e3donline/Motion-System/STPs/MS-X-BELT-PLATE 1.6.step

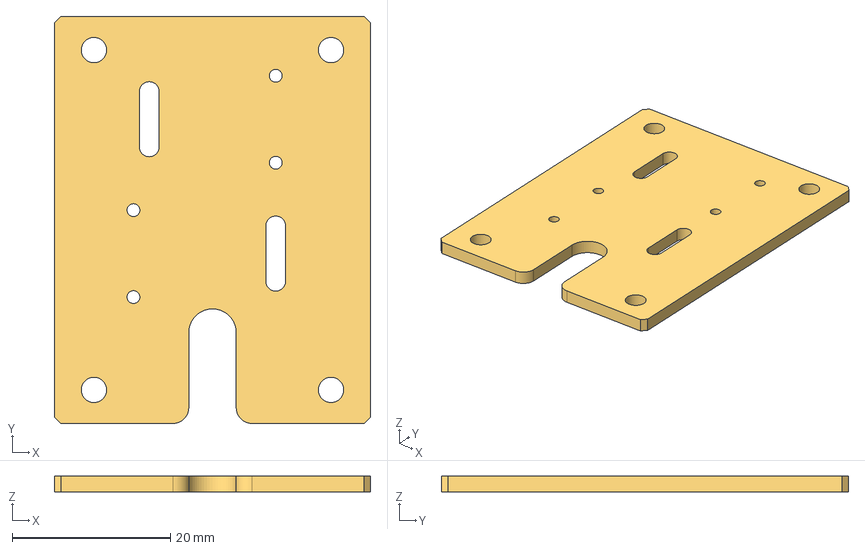
[picture p15: CAD file, 2019-07-30]
STPs/MS-X-BELT-PLATE 1.6.step
40.0 x 51.5 x 2.00 mm
