e3donline/Motion-System/STPs/MS-MOTOR-SPACE-LONG 1.1.step

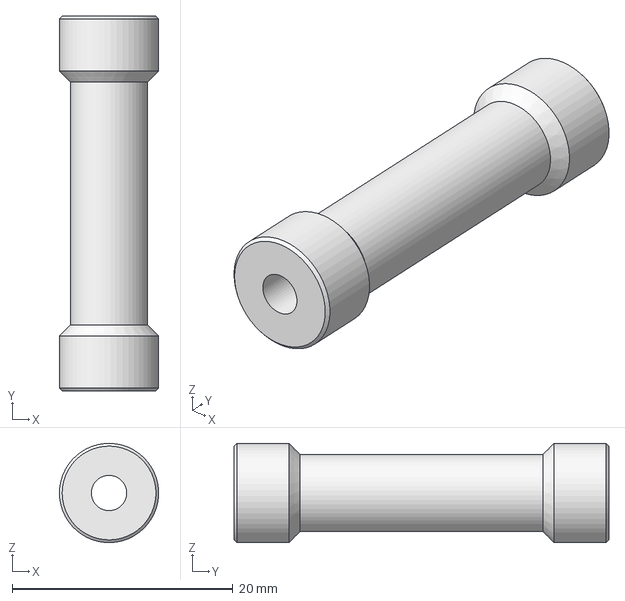
[picture p16: CAD file, 2019-07-30]
STPs/MS-MOTOR-SPACE-LONG 1.1.step
8.99 x 34.0 x 9.00 mm
