e3donline/Motion-System/STPs/MS-TENSION-BLOCK 1.1.step

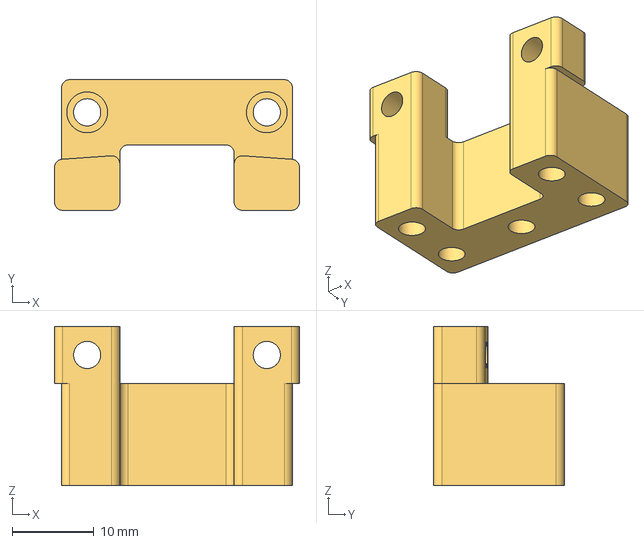
[picture p17: CAD file, 2019-07-30]
STPs/MS-TENSION-BLOCK 1.1.step
30.0 x 16.0 x 19.5 mm
