e3donline/Motion-System/STPs/MS-XY-STOP 1.1.step

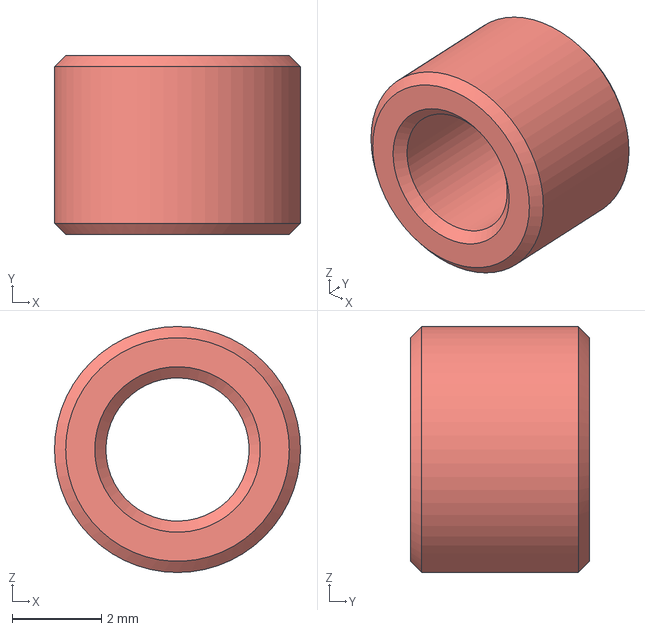
[picture p18: CAD file, 2019-07-30]
STPs/MS-XY-STOP 1.1.step
5.50 x 4.00 x 5.50 mm
