e3donline/Motion-System/STPs/MS-X-BLOCK 1.3.step

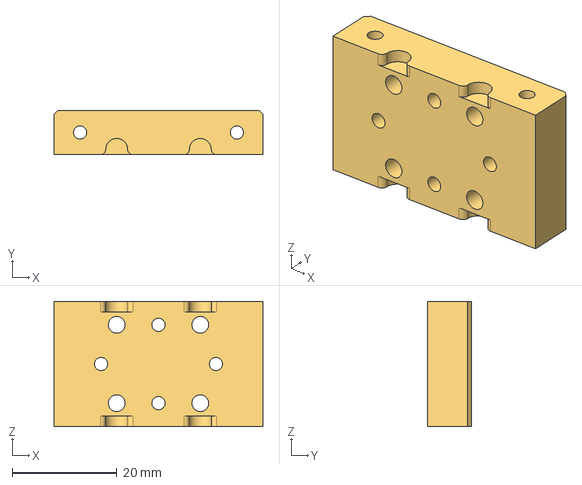
[picture p19: CAD file, 2019-07-30]
STPs/MS-X-BLOCK 1.3.step
40.0 x 8.50 x 24.0 mm
