e3donline/Motion-System/STPs/MS-X-BAR-ALU 1.3.step

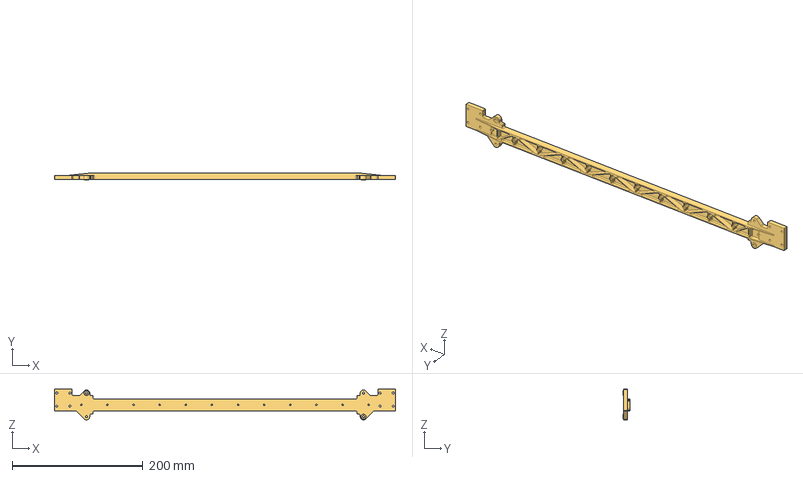
[picture p20: CAD file, 2019-07-30]
STPs/MS-X-BAR-ALU 1.3.step
522.0 x 10.5 x 47.2 mm
