e3donline/Motion-System/STPs/MS-BASE-PLATE 1.4.step

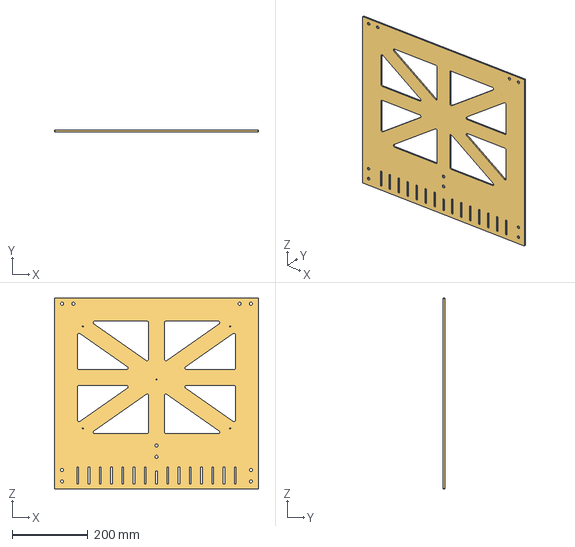
[picture p21: CAD file, 2019-07-30]
STPs/MS-BASE-PLATE 1.4.step
540.0 x 4.00 x 505.0 mm
