e3donline/Motion-System/STPs/MS-BELT-CLAMP-IM 1.2.step

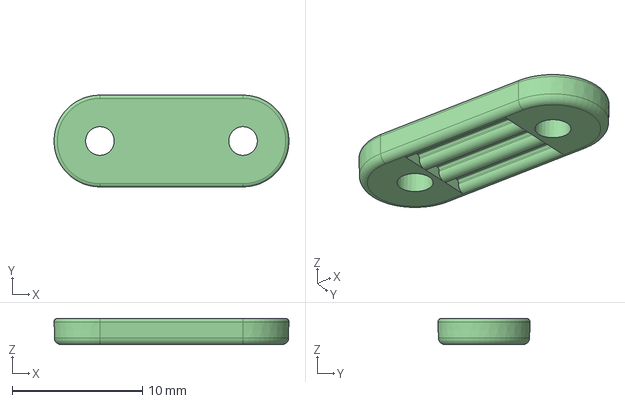
[picture p22: CAD file, 2019-07-30]
STPs/MS-BELT-CLAMP-IM 1.2.step
18.1 x 7.06 x 2.00 mm
