e3donline/Motion-System/STPs/MS-LONG-PULLEY-STANDOFF 1.3.step

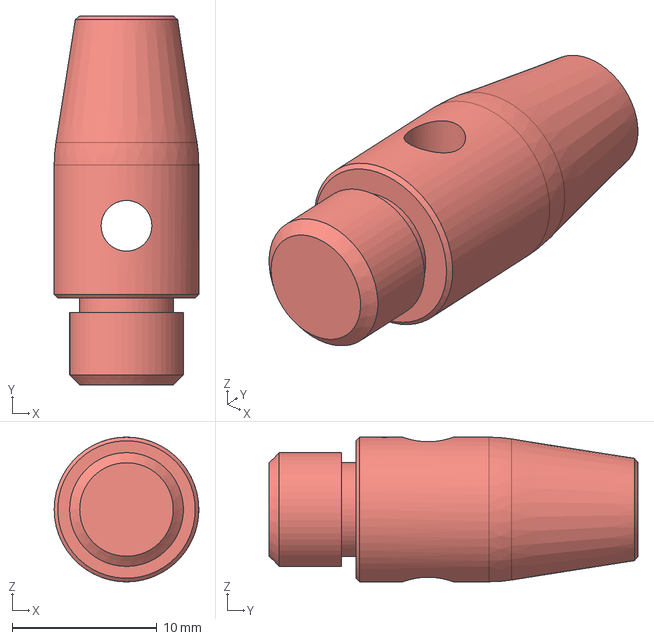
[picture p23: CAD file, 2019-07-30]
STPs/MS-LONG-PULLEY-STANDOFF 1.3.step
10.0 x 25.5 x 10.0 mm
