e3donline/Motion-System/STPs/MS-MOTOR-SPACE-SHORT 1.1.step

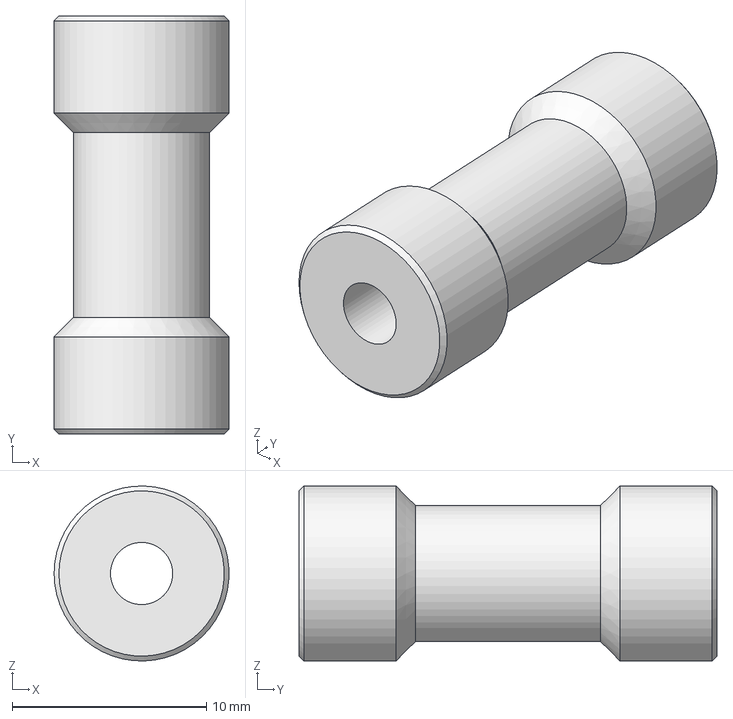
[picture p24: CAD file, 2019-07-30]
STPs/MS-MOTOR-SPACE-SHORT 1.1.step
8.99 x 21.5 x 9.00 mm
