e3donline/Motion-System/STPs/MS-X-SPACER 1.1.step

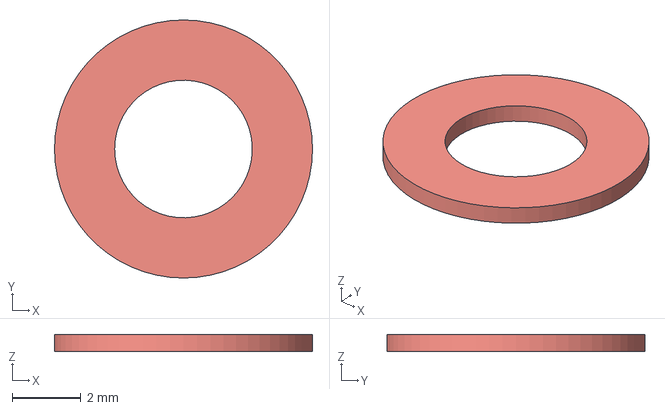
[picture p25: CAD file, 2019-07-30]
STPs/MS-X-SPACER 1.1.step
7.50 x 7.50 x 0.5 mm
