e3donline/Motion-System/STPs/MS-BED-BRACKET 1.4.step

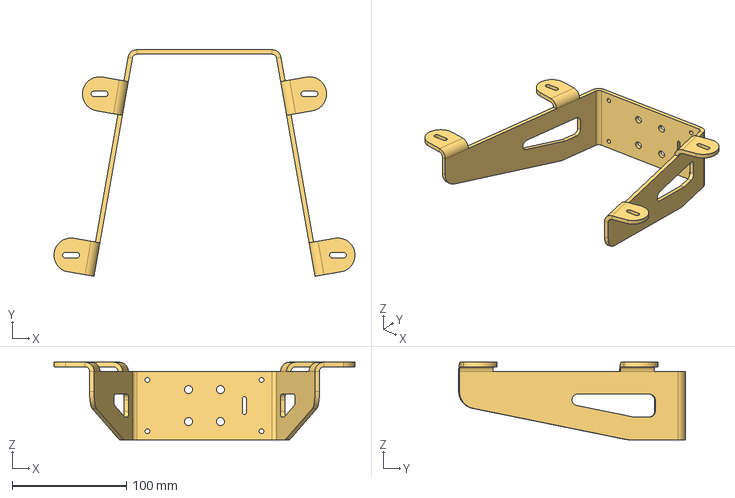
[picture p26: CAD file, 2019-07-30]
STPs/MS-BED-BRACKET 1.4.step
263.8 x 198.6 x 68.0 mm
