e3donline/Motion-System/STPs/MS-SHORT-PULLEY-STANDOFF 1.3.step

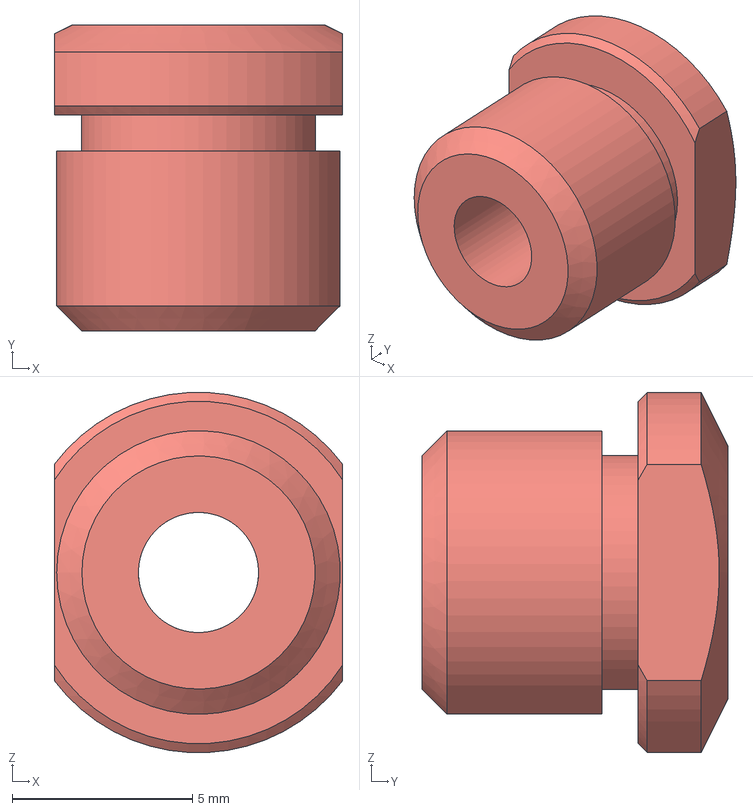
[picture p27: CAD file, 2019-07-30]
STPs/MS-SHORT-PULLEY-STANDOFF 1.3.step
8.00 x 8.50 x 9.99 mm
