e3donline/Motion-System/STPs/MS-Z-STOP 1.0.step

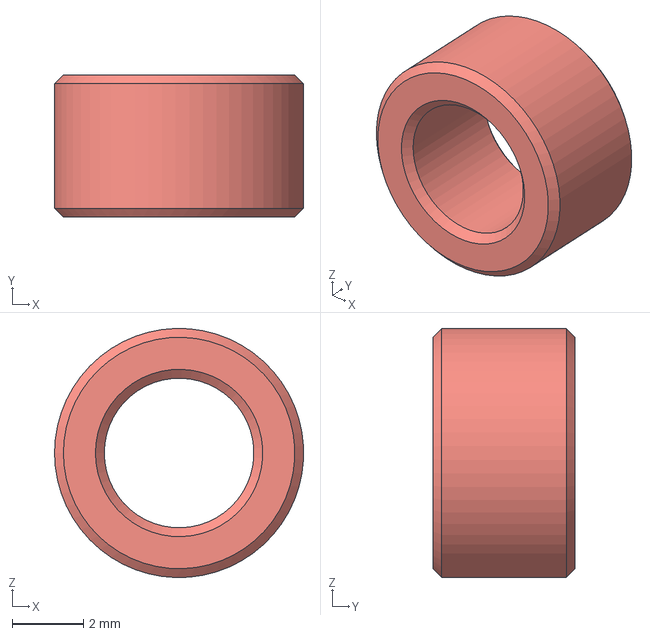
[picture p28: CAD file, 2019-07-30]
STPs/MS-Z-STOP 1.0.step
6.99 x 4.00 x 7.00 mm
