e3donline/Motion-System/STPs/MS-TOP-PLATE 1.6.step

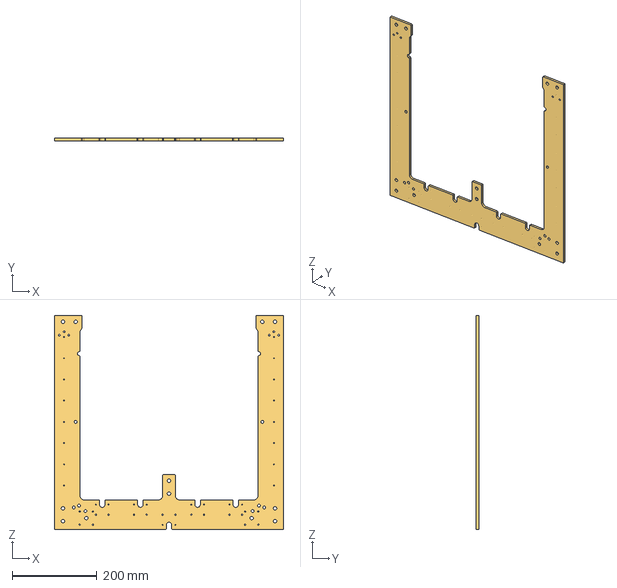
[picture p29: CAD file, 2019-07-30]
STPs/MS-TOP-PLATE 1.6.step
540.0 x 6.00 x 505.0 mm
