e3donline/Motion-System/STPs/MS-TENSION-ARM 1.0.step

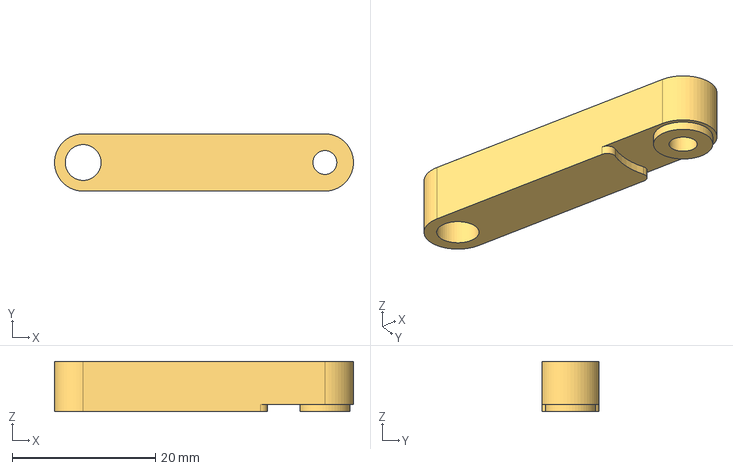
[picture p30: CAD file, 2019-07-30]
STPs/MS-TENSION-ARM 1.0.step
41.8 x 8.00 x 7.00 mm
