e3donline/Motion-System/STPs/MS-Z-MOTOR-BRACKET 1.1.step

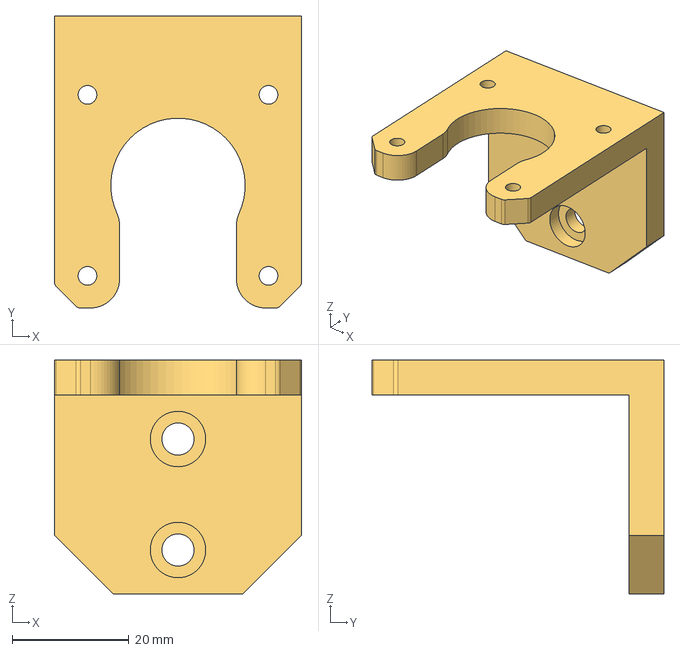
[picture p31: CAD file, 2019-07-30]
STPs/MS-Z-MOTOR-BRACKET 1.1.step
42.3 x 50.0 x 40.0 mm
