e3donline/Motion-System/STPs/MS-BED-PLATE 1.3.step

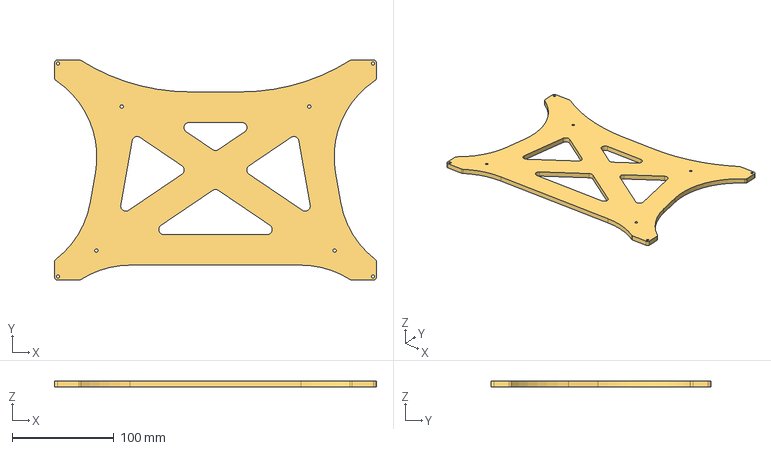
[picture p32: CAD file, 2019-07-30]
STPs/MS-BED-PLATE 1.3.step
316.0 x 216.0 x 6.00 mm
