e3donline/Motion-System/STPs/MS-SOFF-M3-FF-24L 1.1.step

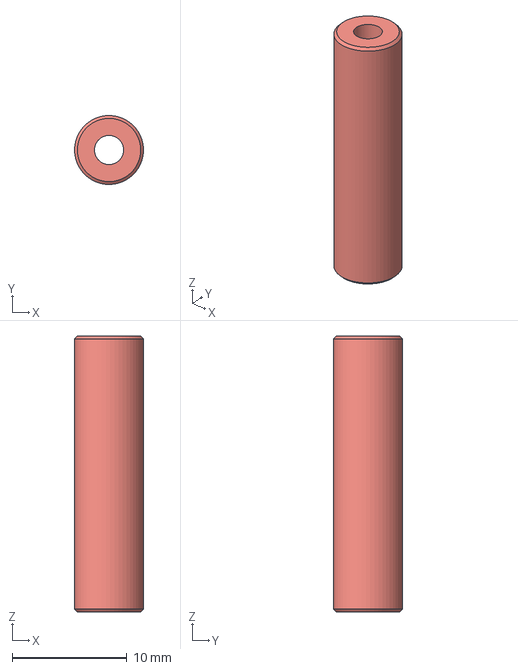
[picture p33: CAD file, 2019-07-30]
STPs/MS-SOFF-M3-FF-24L 1.1.step
5.99 x 6.00 x 24.0 mm
