e3donline/Motion-System/PDFs/MS-SHAFT-BOLT v1.4.pdf

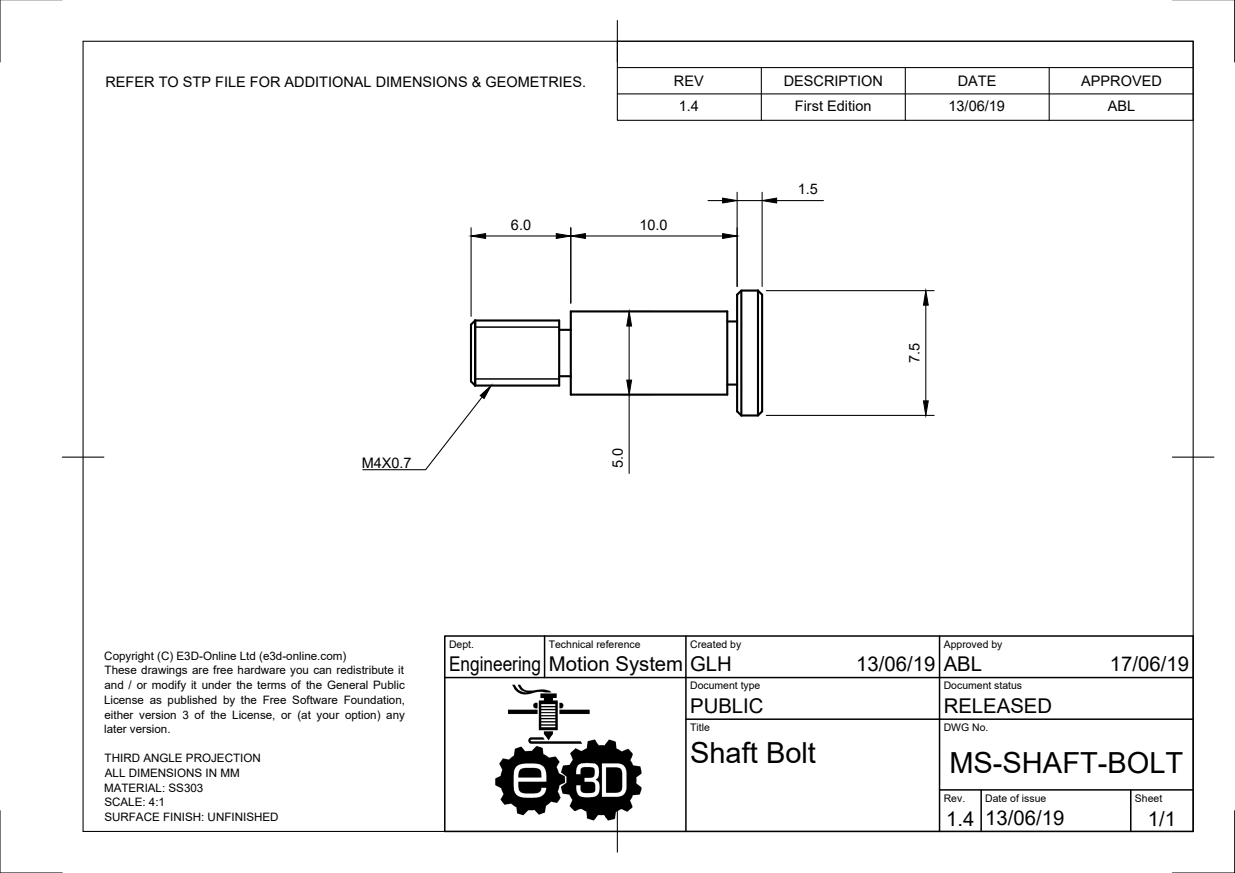
[picture p47: page 1]
First Edition; ABL 7.5

REFER TO STP FILE FOR ADDITIONAL DIMENSIONS & GEOMETRIES.

Dept. Engineering | Technical reference Motion System | Created by GLH 13/06/19 | Approved by ABL Copyright (C) E3D-Online Ltd (e3d-online.com) 17/06/19

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

Document type PUBLIC | Document status RELEASED

Title | DWG No. MS-SHAFT-BOLT Shaft Bolt

THIRD ANGLE PROJECTION
ALL DIMENSIONS IN MM
MATERIAL: SS303
SCALE: 4:1
SURFACE FINISH: UNFINISHED

Rev. 1.4 | Date of issue 13/06/19 | Sheet 1/1
