e3donline/Motion-System/PDFs/MS-TENSION-ARM v1.0.pdf

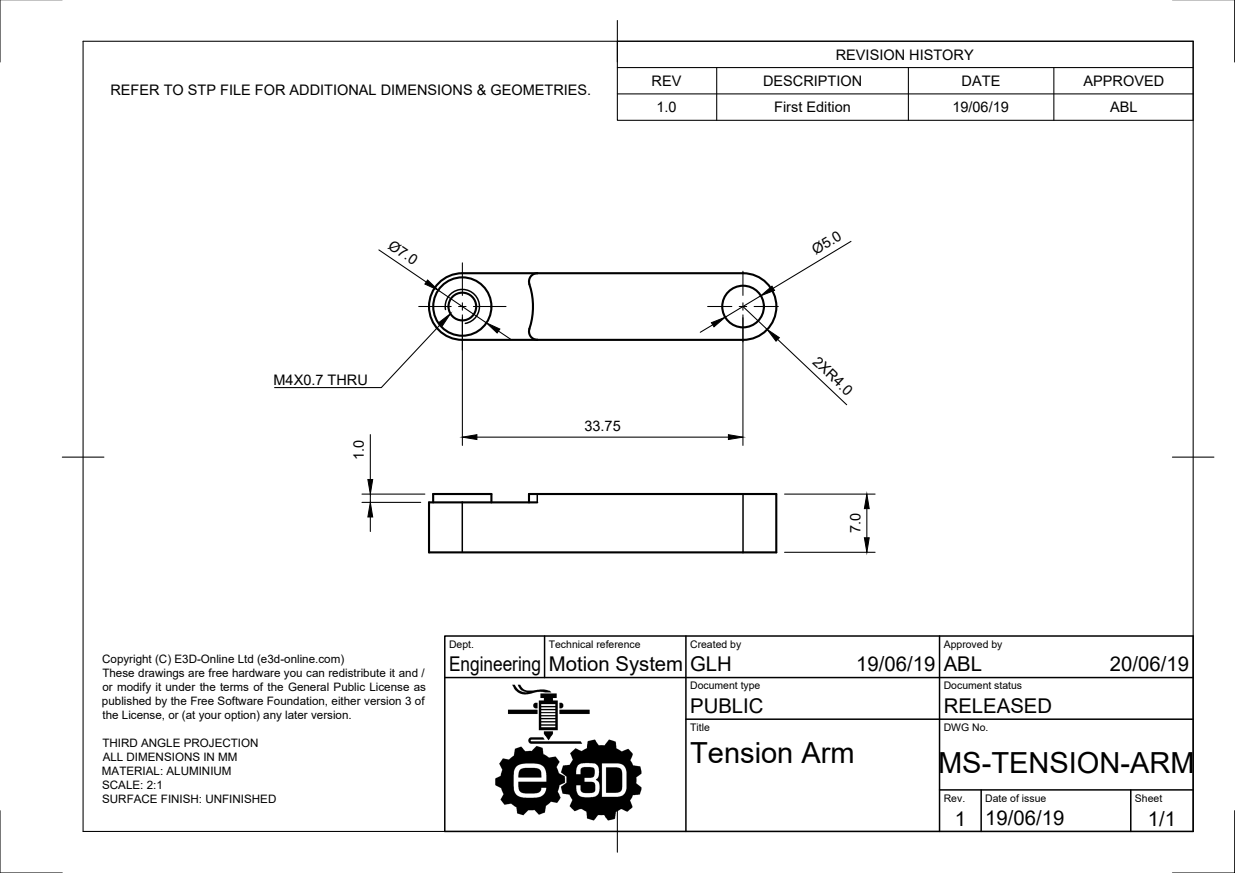
[picture p48: page 1]
M4X0.7 THRU

REVISION HISTORY

REV | DESCRIPTION | DATE | APPROVED
1.0 | First Edition | 19/06/19 | ABL

REFER TO STP FILE FOR ADDITIONAL DIMENSIONS & GEOMETRIES.

Dept. Engineering | Technical reference Motion System | Created by GLH 19/06/19 | Approved by ABL 20/06/19

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

Document type PUBLIC | Document status RELEASED

the License, or (at your option) any later version.

Title Tension Arm | DWG No. MS-TENSION-ARM

THIRD ANGLE PROJECTION
ALL DIMENSIONS IN MM
MATERIAL: ALUMINIUM
SCALE: 2:1
SURFACE FINISH: UNFINISHED

Rev. 1 | Date of issue 19/06/19 | Sheet 1/1
