e3donline/Motion-System/PDFs/MS-TOP-PLATE v1.6.pdf

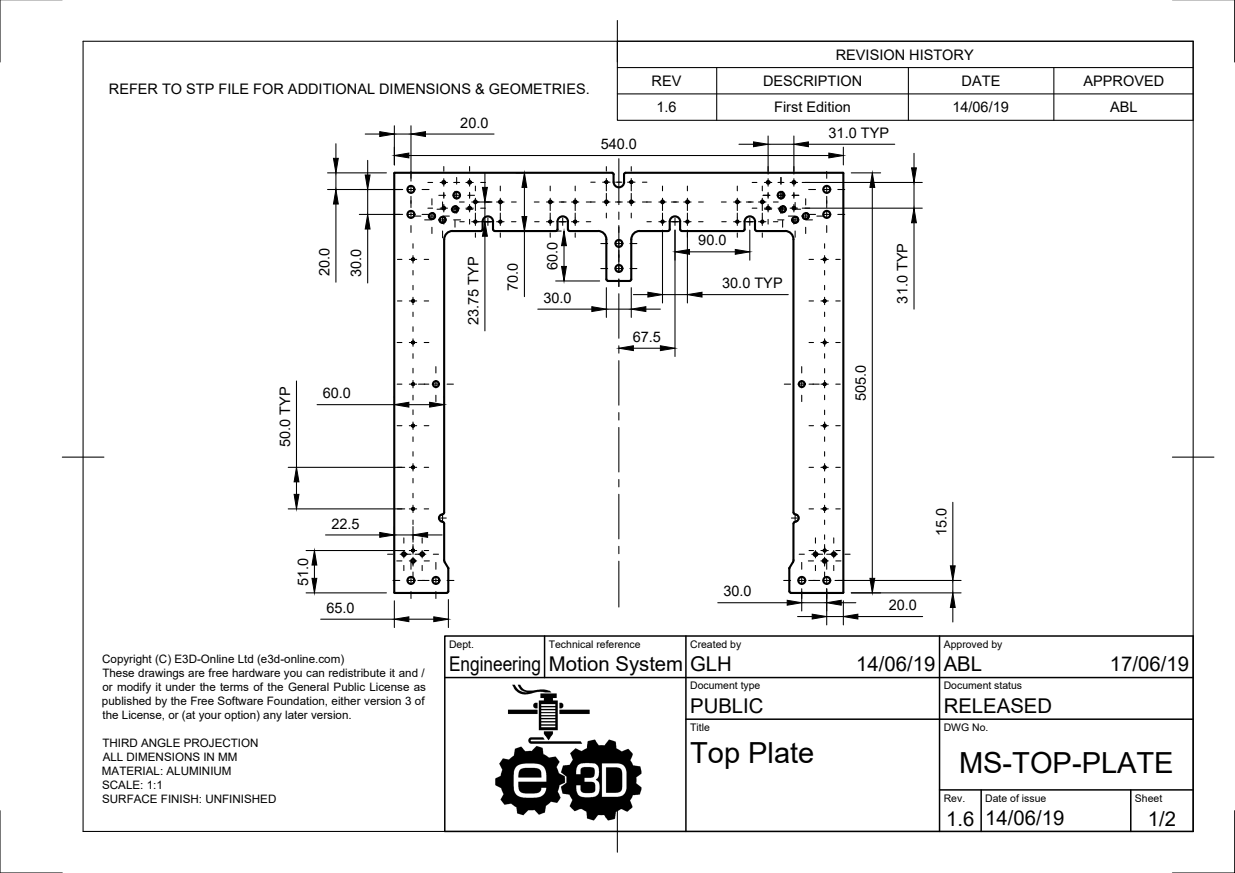
[picture p49: page 1]
90.0 50.0 TYP; 67.5 60.0 23.75 TYP

REVISION HISTORY

REV | DESCRIPTION | DATE | APPROVED
1.6 | First Edition | 14/06/19 | ABL

REFER TO STP FILE FOR ADDITIONAL DIMENSIONS & GEOMETRIES.

31.0 TYP 31.0 TYP 30.0 TYP

Dept. Engineering | Technical reference Motion System | Created by GLH 14/06/19 | Approved by ABL 17/06/19

Copyright (C) E3D-Online Ltd (e3d-online.com)
These drawings are free hardware you can redistribute it and / or modify it under the terms of the General Public License as published by the Free Software Foundation, either version 3 of

Document type PUBLIC | Document status RELEASED

the License, or (at your option) any later version.

Title | DWG No. MS-TOP-PLATE Top Plate

THIRD ANGLE PROJECTION
ALL DIMENSIONS IN MM
MATERIAL: ALUMINIUM
SCALE: 1:1
SURFACE FINISH: UNFINISHED

Rev. 1.6 | Date of issue 14/06/19 | Sheet 1/2

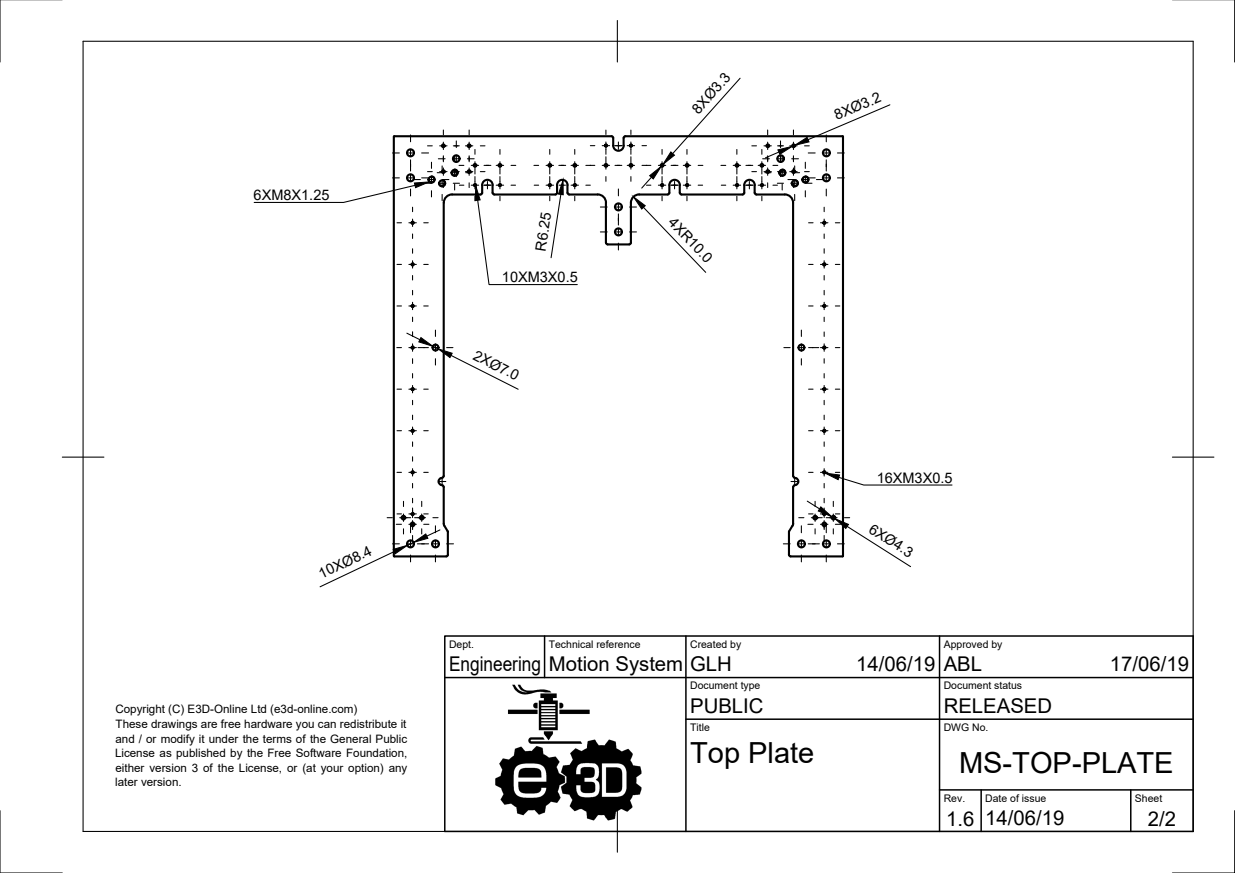
[picture p50: page 2]
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

Document type PUBLIC | Document status RELEASED

Copyright (C) E3D-Online Ltd (e3d-online.com)
These drawings are free hardware you can redistribute it
and / or modify it under the terms of the General Public
License as published by the Free Software Foundation,
either version 3 of the License, or (at your option) any
later version.

Title | DWG No. MS-TOP-PLATE Top Plate

Rev. 1.6 | Date of issue 14/06/19 | Sheet 2/2
