e3donline/Motion-System/PDFs/MS-Z-NUT-BRACKET v1.3.pdf

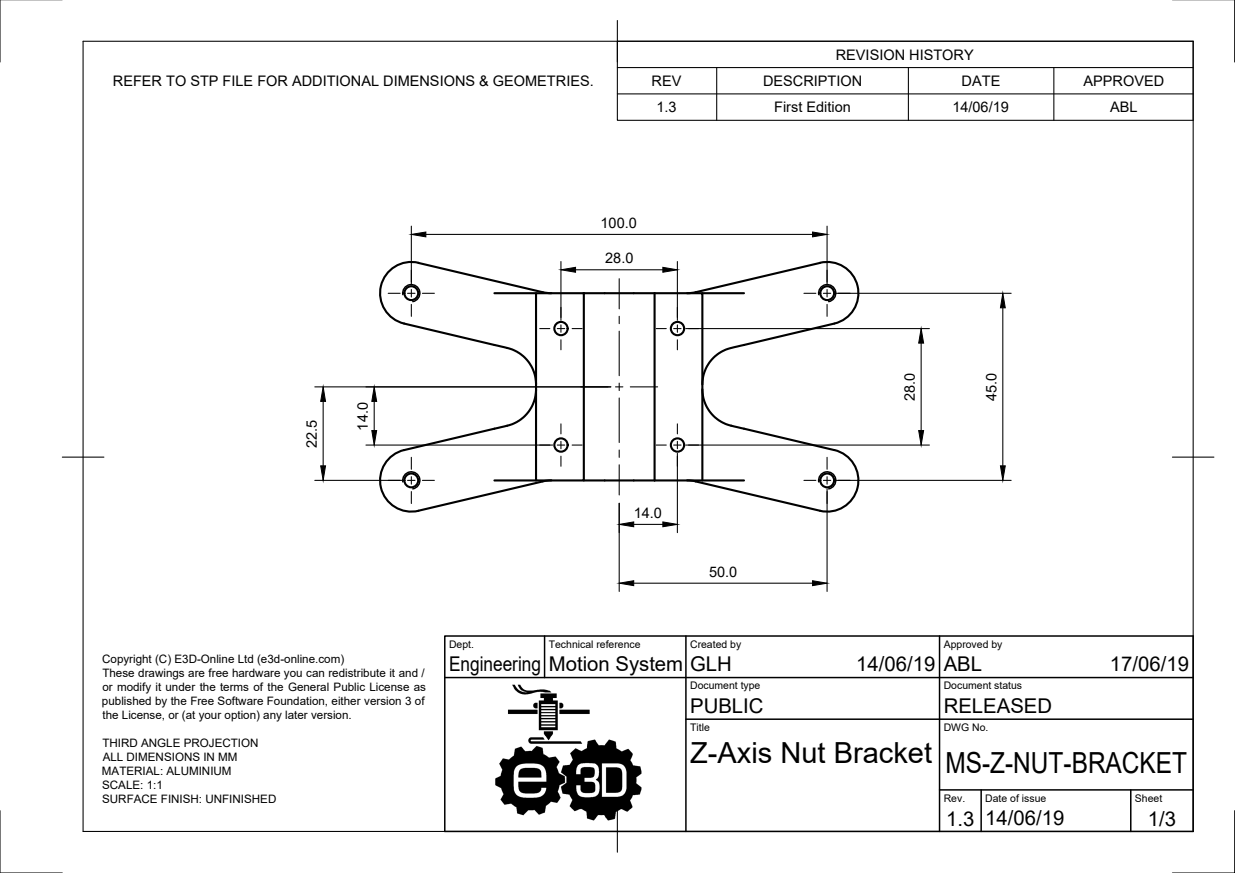
[picture p51: page 1]

REVISION HISTORY

REFER TO STP FILE FOR ADDITIONAL DIMENSIONS & GEOMETRIES.

REV | DESCRIPTION | DATE | APPROVED
1.3 | First Edition | 14/06/19 | ABL

Dept. Engineering | Technical reference Motion System | Created by GLH 14/06/19 | Approved by ABL 17/06/19

Copyright (C) E3D-Online Ltd (e3d-online.com)
These drawings are free hardware you can redistribute it and / or modify it under the terms of the General Public License as published by the Free Software Foundation, either version 3 of

Document type PUBLIC | Document status RELEASED

the License, or (at your option) any later version.

Title | DWG No. MS-Z-NUT-BRACKET Z-Axis Nut Bracket

THIRD ANGLE PROJECTION
ALL DIMENSIONS IN MM
MATERIAL: ALUMINIUM
SCALE: 1:1
SURFACE FINISH: UNFINISHED

Rev. 1.3 | Date of issue 14/06/19 | Sheet

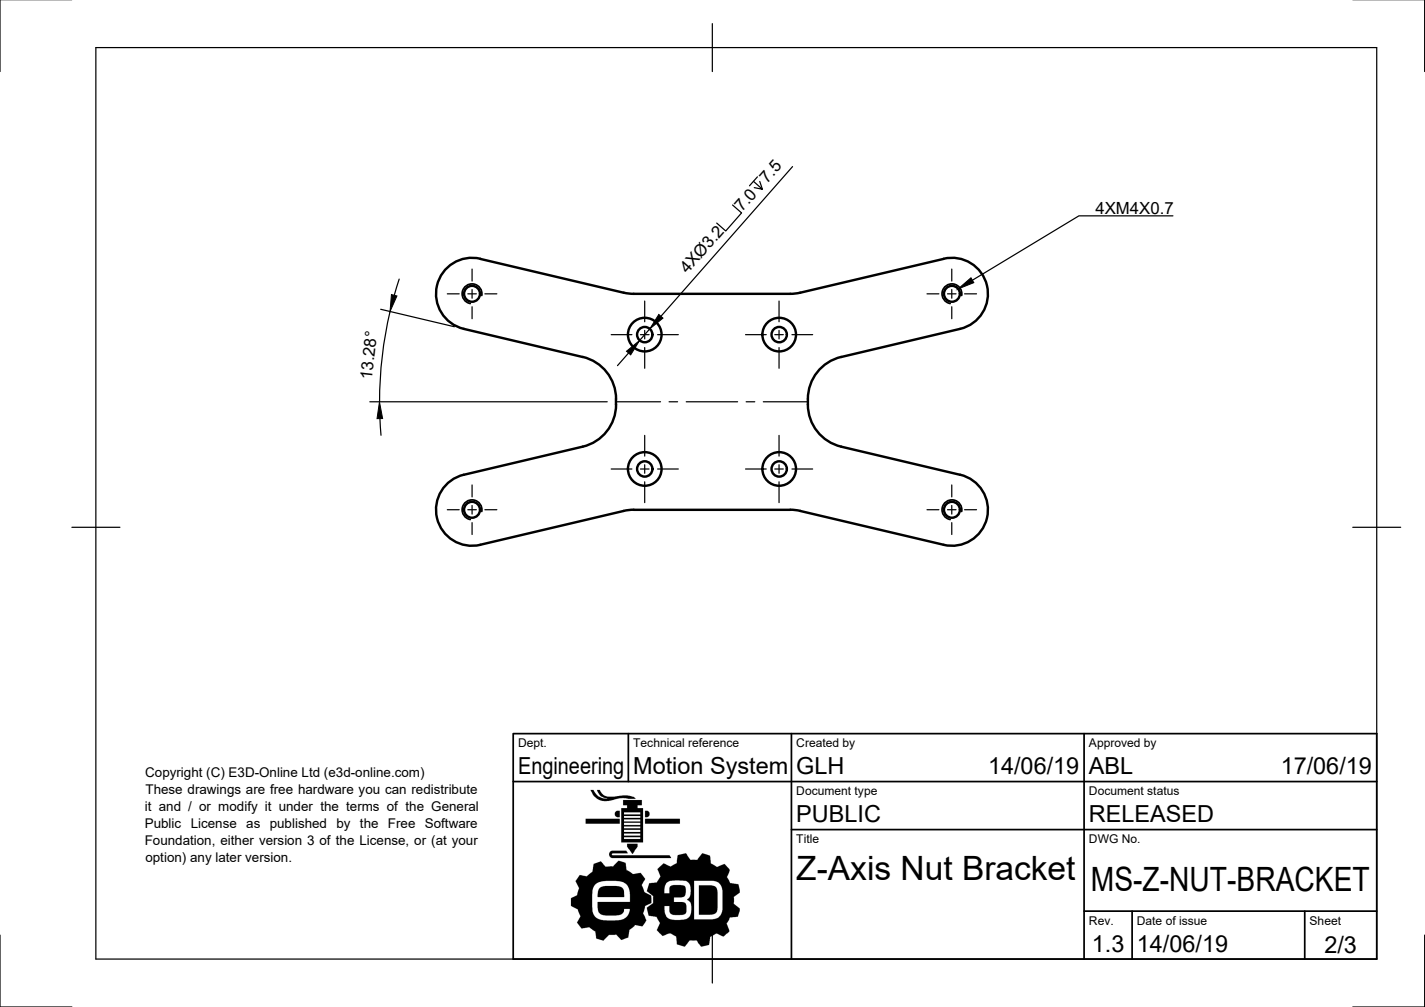
[picture p52: page 2]
Copyright (C) E3D-Online Ltd (e3d-online.com); Engineering; Motion System; GLH; ABL

Dept. | Technical reference | Created by 14/06/19 | Approved by 17/06/19

These drawings are free hardware you can redistribute
it and / or modify it under the terms of the General
Public License as published by the Free Software
Foundation, either version 3 of the License, or (at your
option) any later version.

Document type PUBLIC | Document status RELEASED

Title | DWG No. MS-Z-NUT-BRACKET Z-Axis Nut Bracket

Rev. | Date of issue | Sheet

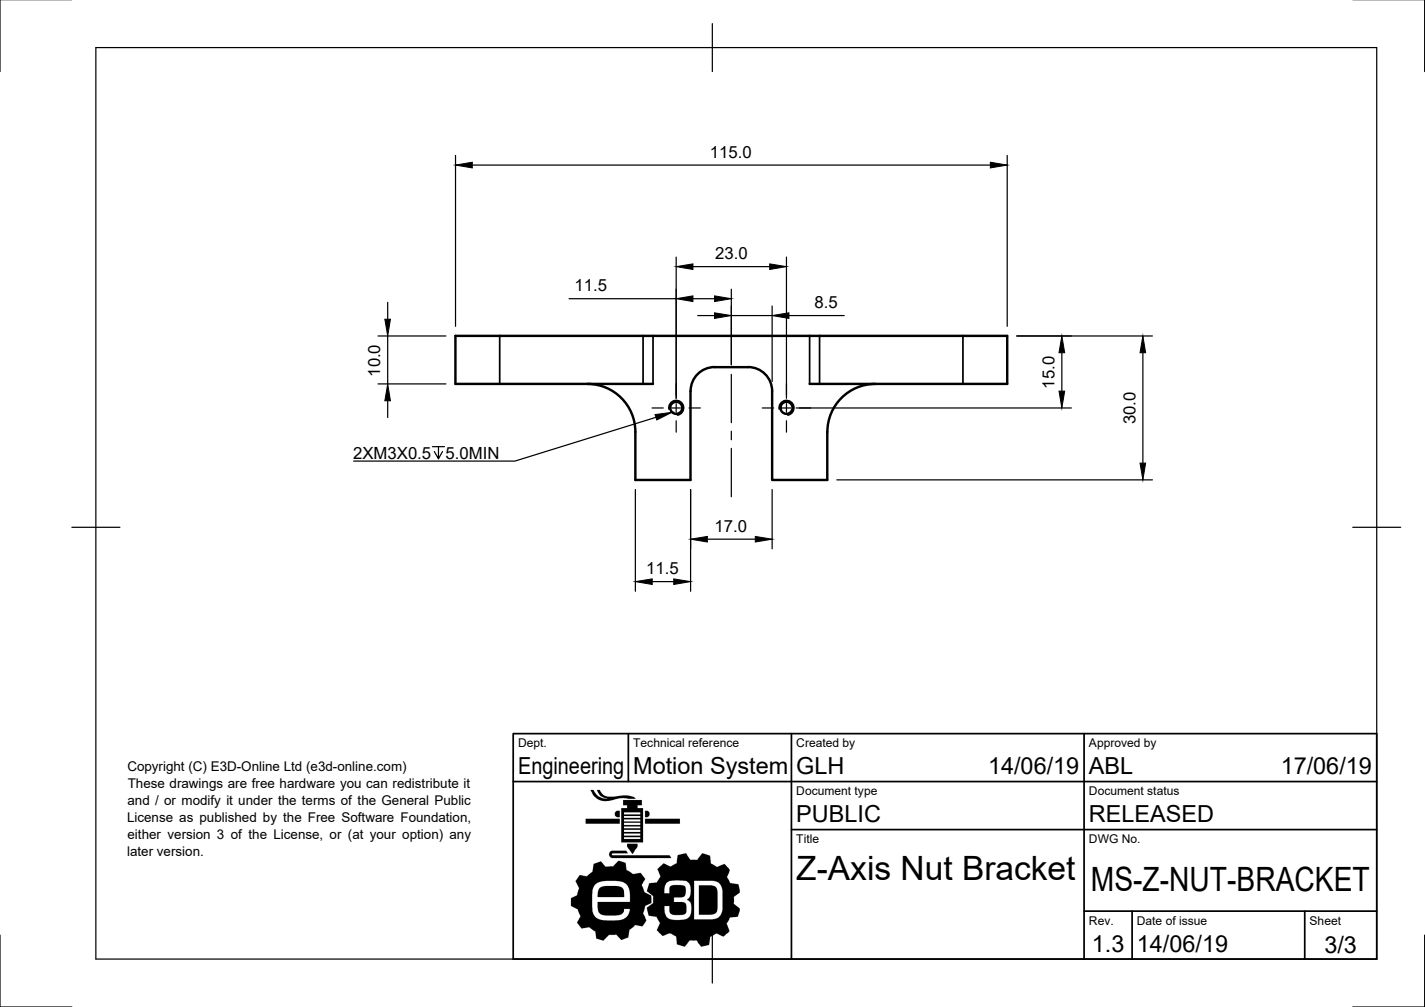
[picture p53: page 3]
Copyright (C) E3D-Online Ltd (e3d-online.com); Engineering; Motion System; GLH; ABL; later version.; 2XM3X0.5 5.0MIN

Dept. | Technical reference | Created by 14/06/19 | Approved by 17/06/19

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

Document type PUBLIC | Document status RELEASED

Title | DWG No. MS-Z-NUT-BRACKET Z-Axis Nut Bracket

Rev. | Date of issue | Sheet
