e3donline/Motion-System/PDFs/MS-REAR-PANEL v1.0.pdf

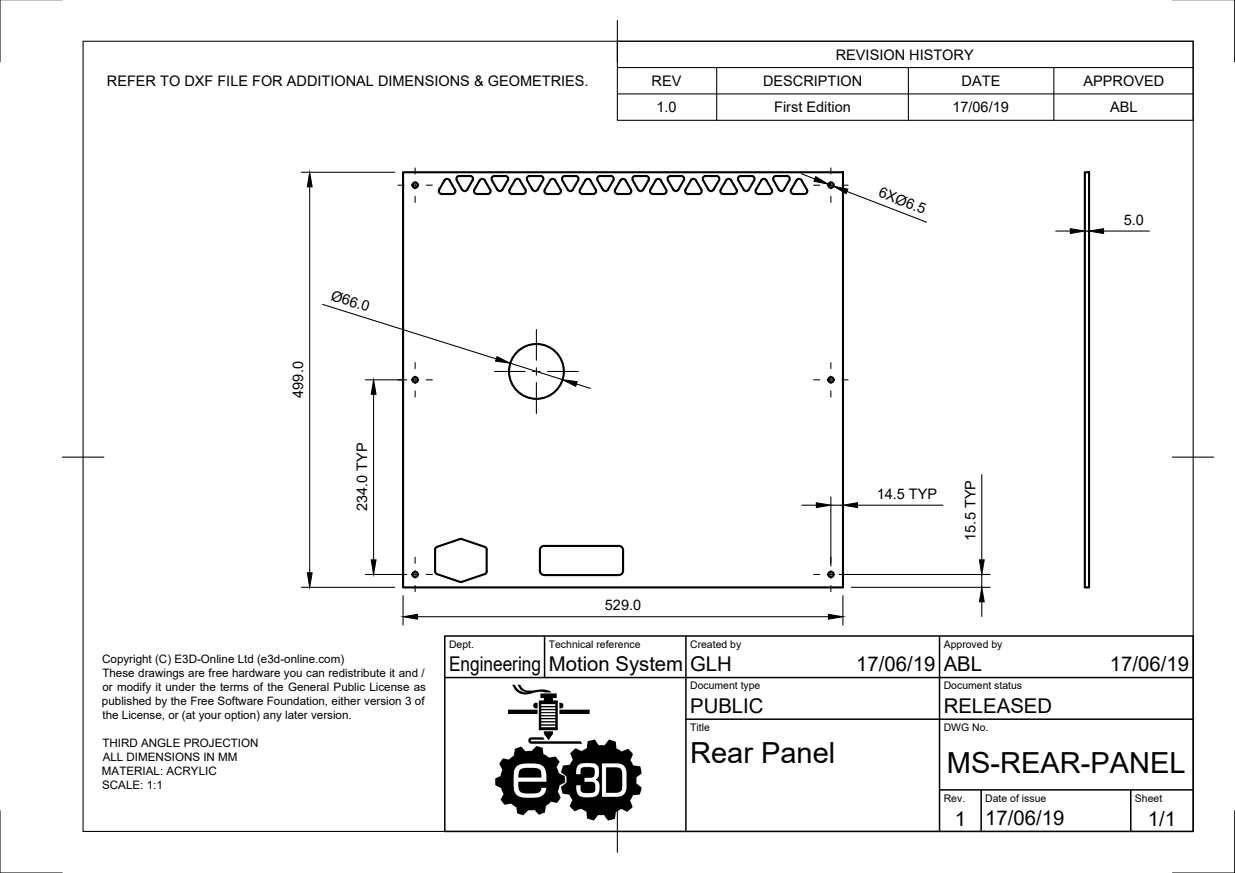
[picture p56: page 1]
SCALE: 1:1; 15.5 TYP14.5 TYP 234.0 TYP

REVISION HISTORY

REFER TO DXF FILE FOR ADDITIONAL DIMENSIONS & GEOMETRIES.

REV | DESCRIPTION | DATE | APPROVED
1.0 | First Edition | 17/06/19 | ABL

Dept. Engineering | Technical reference Motion System | Created by GLH 17/06/19 | Approved by ABL 17/06/19

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

Document type PUBLIC | Document status RELEASED

the License, or (at your option) any later version.

Title Rear Panel | DWG No. MS-REAR-PANEL

THIRD ANGLE PROJECTION
ALL DIMENSIONS IN MM
MATERIAL: ACRYLIC

Rev. 1 | Date of issue 17/06/19 | Sheet 1/1
