e3donline/Motion-System/PDFs/MS-SIDE-PANEL v1.0.pdf

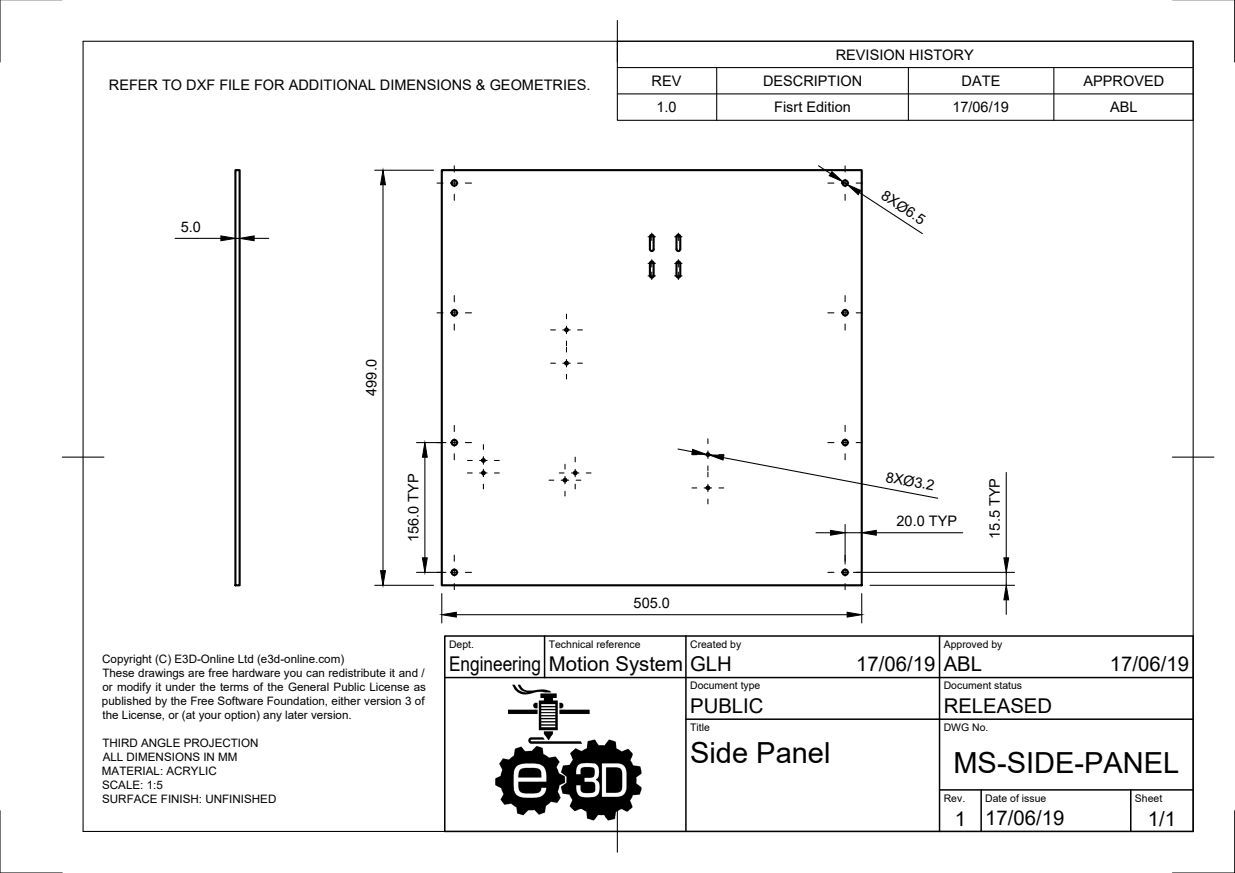
[picture p57: page 1]

REVISION HISTORY

REV | DESCRIPTION | DATE | APPROVED
1.0 | Fisrt Edition | 17/06/19 | ABL

REFER TO DXF FILE FOR ADDITIONAL DIMENSIONS & GEOMETRIES. 499.0

8XØ3.2 15.5 TYP 20.0 TYP 156.0 TYP

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

Document type PUBLIC | Document status RELEASED

the License, or (at your option) any later version.

Title | DWG No. MS-SIDE-PANEL Side Panel

THIRD ANGLE PROJECTION
ALL DIMENSIONS IN MM
MATERIAL: ACRYLIC
SCALE: 1:5
SURFACE FINISH: UNFINISHED

Rev. 1 | Date of issue 17/06/19 | Sheet 1/1
