e3donline/Motion-System/PDFs/MS-X-BAR-ALU v1.3.pdf

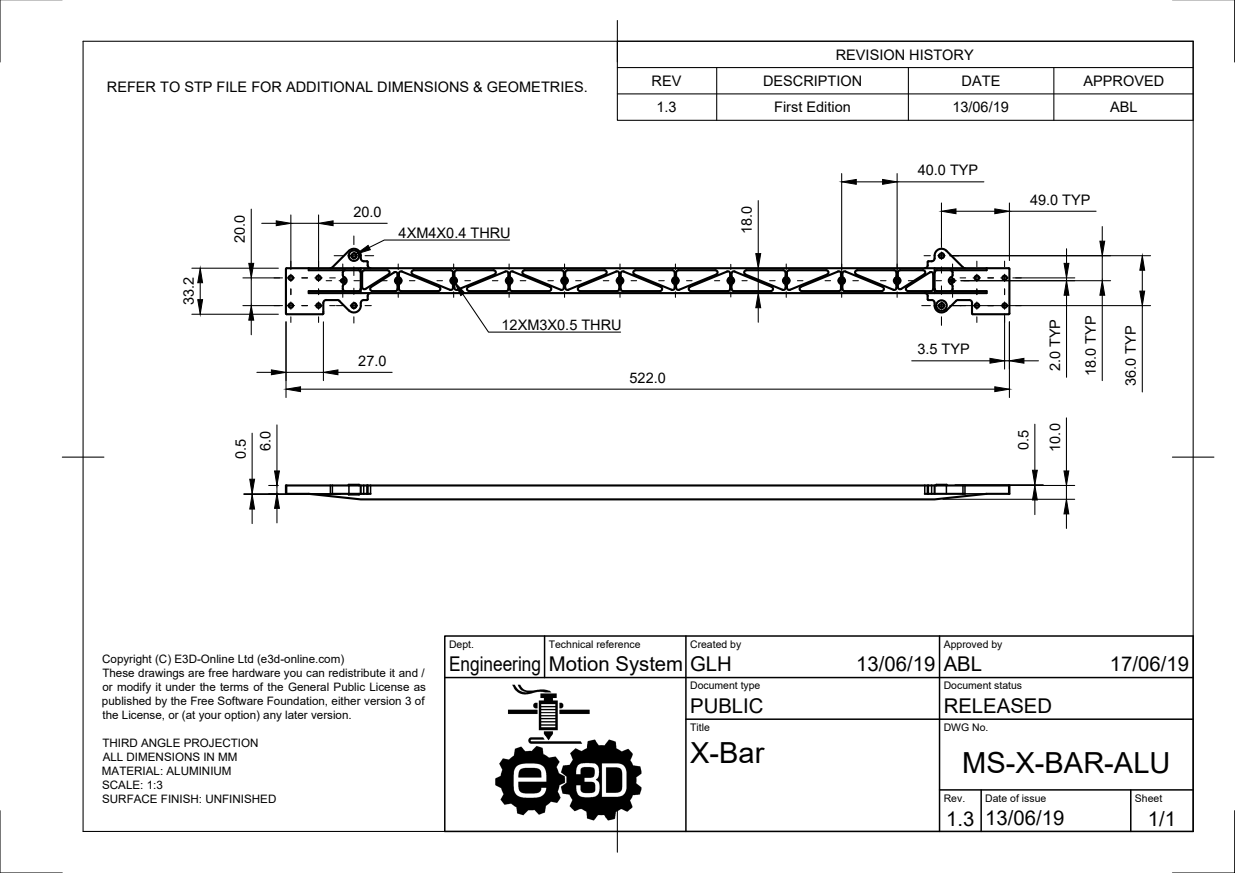
[picture p58: page 1]
4XM4X0.4 THRU; 12XM3X0.5 THRU; 40.0 TYP; 36.0 TYP 18.0 TYP 522.0; 2.0 TYP 3.5 TYP; 49.0 TYP

REVISION HISTORY

REV | DESCRIPTION | DATE | APPROVED
1.3 | First Edition | 13/06/19 | ABL

REFER TO STP FILE FOR ADDITIONAL DIMENSIONS & GEOMETRIES. 33.2

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

Document type PUBLIC | Document status RELEASED

the License, or (at your option) any later version.

Title X-Bar | DWG No. MS-X-BAR-ALU

THIRD ANGLE PROJECTION
ALL DIMENSIONS IN MM
MATERIAL: ALUMINIUM
SCALE: 1:3
SURFACE FINISH: UNFINISHED

Rev. 1.3 | Date of issue 13/06/19 | Sheet 1/1
